ju57in3/Internship_Project/image-33.png

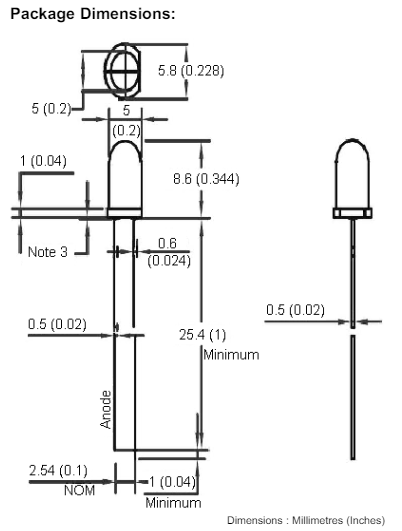
image-33.png
