ju57in3/Internship_Project/Project/extansion_board_v1/boostpck.kicad_sch

## KiCad design Project/extansion_board_v1/boostpck.kicad_sch (2024-04-29, last stored version)

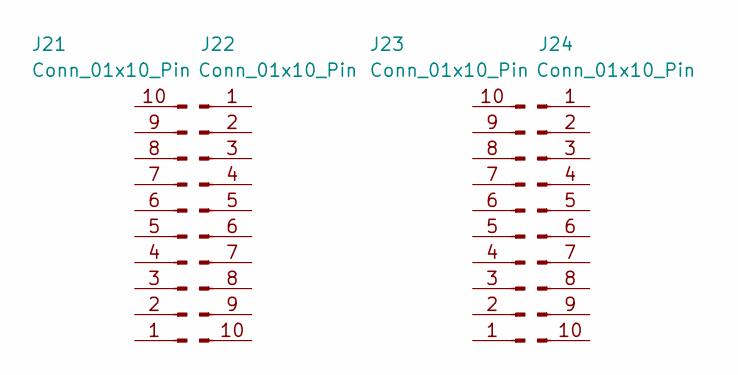
[picture p33: schematic boostpck.kicad_sch]

Parts:
J21, J22, J23, J24: Conn_01x10_Pin
