ju57in3/Internship_Project/Project/extansion_board_v1/deb_circ.kicad_sch

## KiCad design Project/extansion_board_v1/deb_circ.kicad_sch (2024-04-29, last stored version)

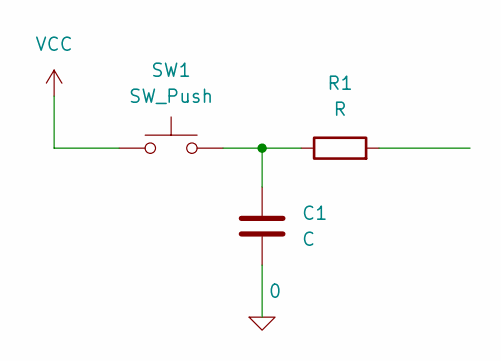
[picture p34: schematic deb_circ.kicad_sch]

Parts:
C1: C
R1: R
SW1: SW_Push

Connections:
0: C1.2
unnamed: C1.1, R1.1, SW1.2
VCC: SW1.1
