ju57in3/Internship_Project/Project/extansion_board_v1/esp32.kicad_sch

## KiCad design Project/extansion_board_v1/esp32.kicad_sch (2024-04-29, last stored version)

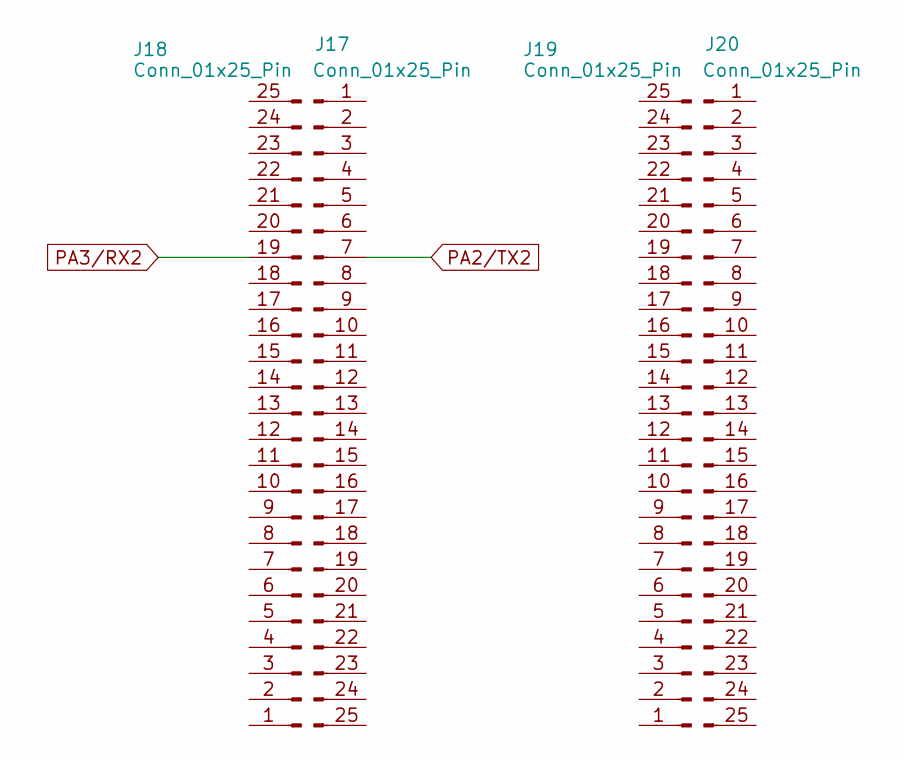
[picture p35: schematic esp32.kicad_sch]

Parts:
J17, J18, J19, J20: Conn_01x25_Pin

Connections:
PA2/TX2: J17.7
PA3/RX2: J18.19
