ju57in3/Internship_Project/Project/extansion_board_v1/extansion_board_v1.kicad_sch

## KiCad design Project/extansion_board_v1/extansion_board_v1.kicad_sch (2024-04-29, last stored version)

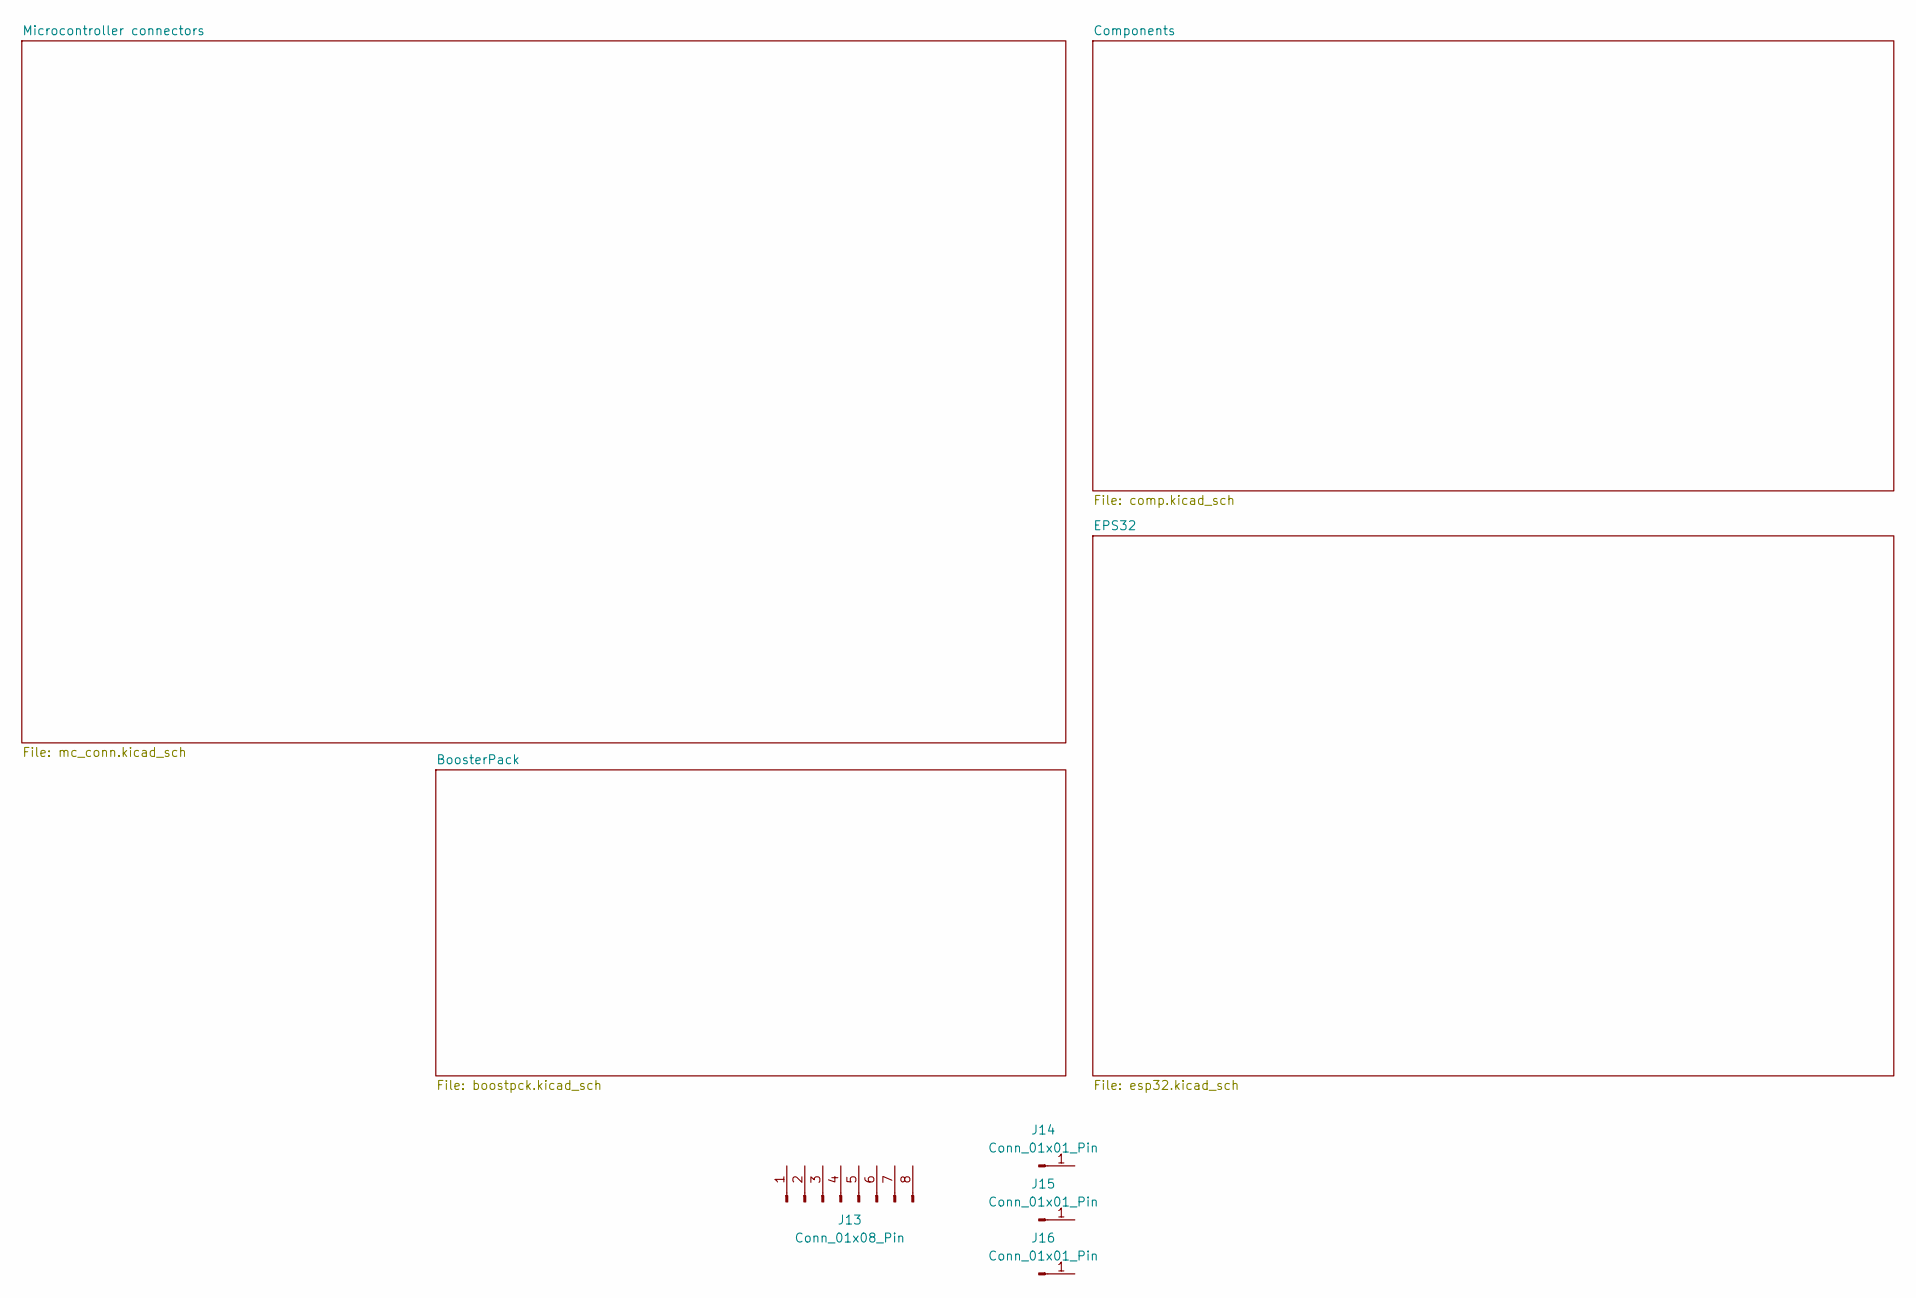
[picture p36: schematic extansion_board_v1.kicad_sch]

Parts:
J13: Conn_01x08_Pin
J14, J15, J16: Conn_01x01_Pin
