ju57in3/Internship_Project/Project/extansion_board_v1/leds_circ.kicad_sch

## KiCad design Project/extansion_board_v1/leds_circ.kicad_sch (2024-04-29, last stored version)

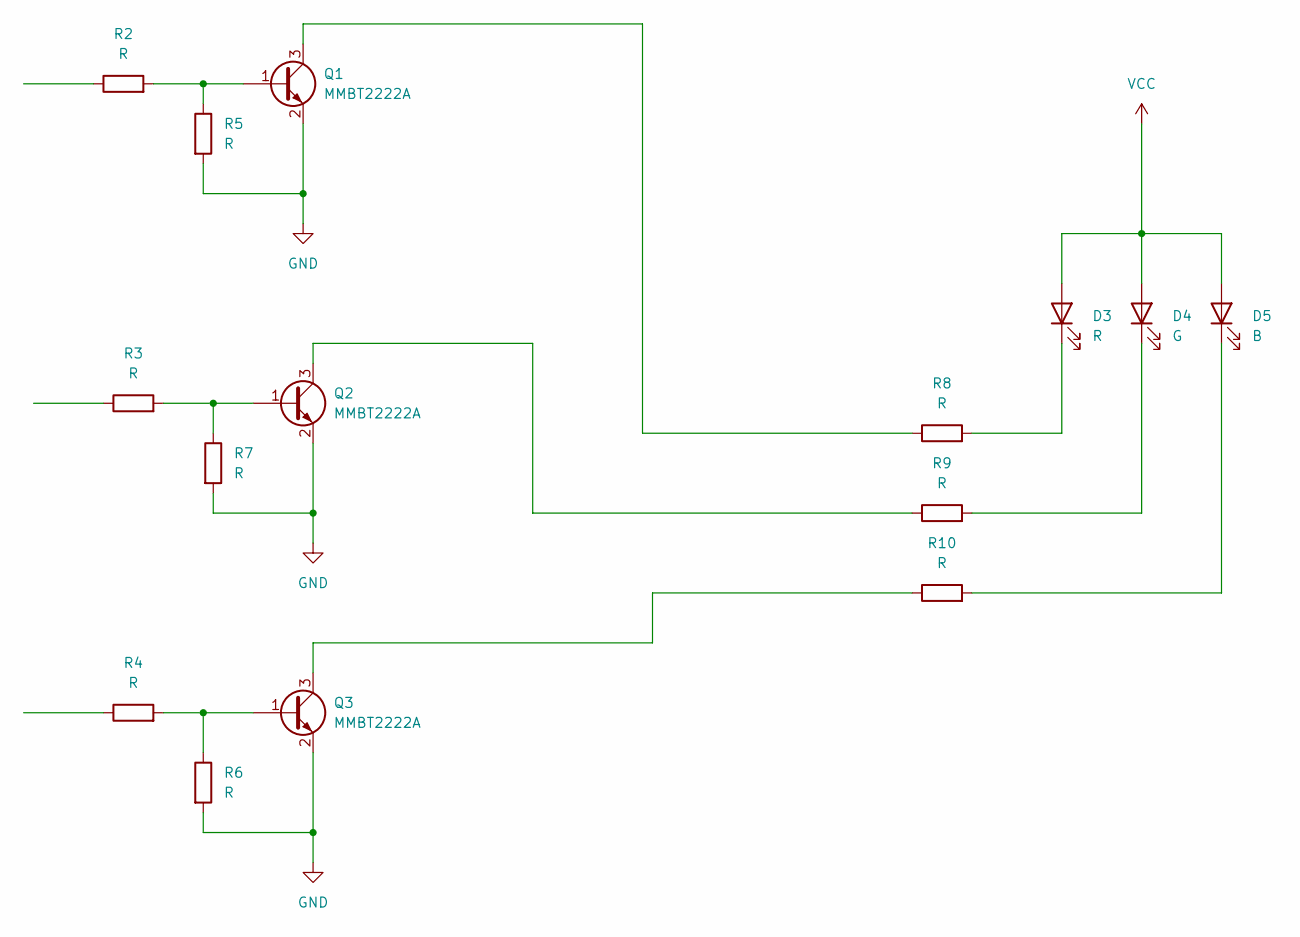
[picture p37: schematic leds_circ.kicad_sch]

Parts:
D3: R
D4: G
D5: B
Q1, Q2, Q3: MMBT2222A; SOT-23
R2, R3, R4, R5, R6, R7, R8, R9, R10: R

Connections:
GND: Q1.2 (E), Q2.2 (E), Q3.2 (E), R5.2, R6.2, R7.2
unnamed: D3.1 (K), R8.2
unnamed: D4.1 (K), R9.2
unnamed: D5.1 (K), R10.2
unnamed: Q1.1 (B), R2.2, R5.1
unnamed: Q1.3 (C), R8.1
unnamed: Q2.1 (B), R3.2, R7.1
unnamed: Q2.3 (C), R9.1
unnamed: Q3.1 (B), R4.2, R6.1
unnamed: Q3.3 (C), R10.1
VCC: D3.2 (A), D4.2 (A), D5.2 (A)
