ju57in3/Internship_Project/Project/extansion_board_v1/mc_conn.kicad_sch

## KiCad design Project/extansion_board_v1/mc_conn.kicad_sch (2024-04-29, last stored version)

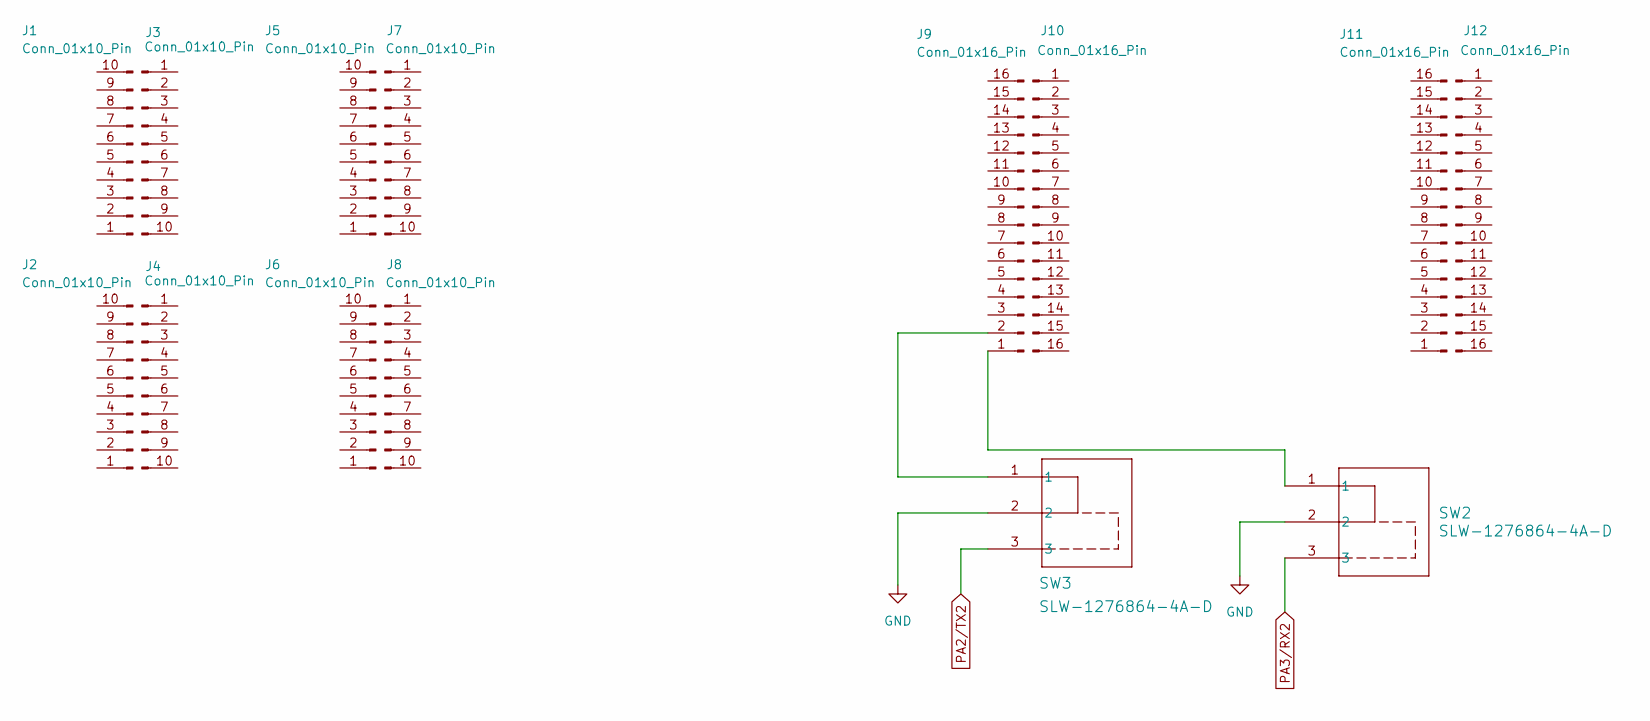
[picture p38: schematic mc_conn.kicad_sch]

Parts:
J1, J2, J3, J4, J5, J6, J7, J8: Conn_01x10_Pin
J9, J10, J11, J12: Conn_01x16_Pin
SW2, SW3: SLW-1276864-4A-D; SLW-1276864_CUD

Connections:
GND: SW2.2, SW3.2
unnamed: J9.1, SW2.1
unnamed: J9.2, SW3.1
PA2/TX2: SW3.3
PA3/RX2: SW2.3
