ju57in3/Internship_Project/Project/extansion_board_v1/temp_sens.kicad_sch

## KiCad design Project/extansion_board_v1/temp_sens.kicad_sch (2024-04-29, last stored version)

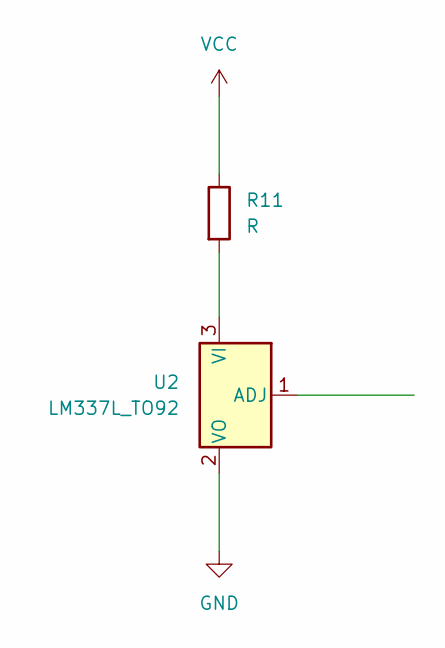
[picture p39: schematic temp_sens.kicad_sch]

Parts:
R11: R
U2: LM337L_TO92; TO-92_Inline

Connections:
GND: U2.2 (VO)
unnamed: R11.2, U2.3 (VI)
VCC: R11.1
